rushabhcodes/turncount/enclosure/output/preview-exploded.png

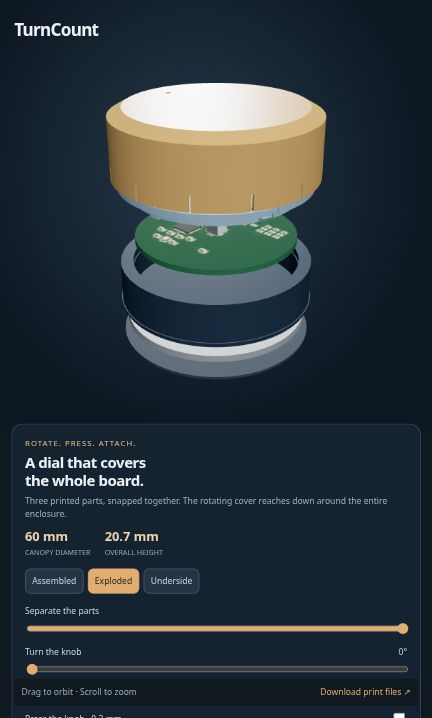
enclosure/output/preview-exploded.png
